trebb/keytee/firmware/keymap_keytee.c

#include "keymap_common.h"

const uint8_t PROGMEM keymaps[][MATRIX_ROWS][MATRIX_COLS] = {
    [0] = KEYMAP(
                 0,
                 1,
                 2,
                 3,
                 4,
                 5,
                 6,
                 7,
                 8,
                 9),
};

const uint16_t PROGMEM fn_actions[] = {
};
